lsd-maddrive/bb_project/Чертежи/solid/Крепление переходника 4S.SLDPRT

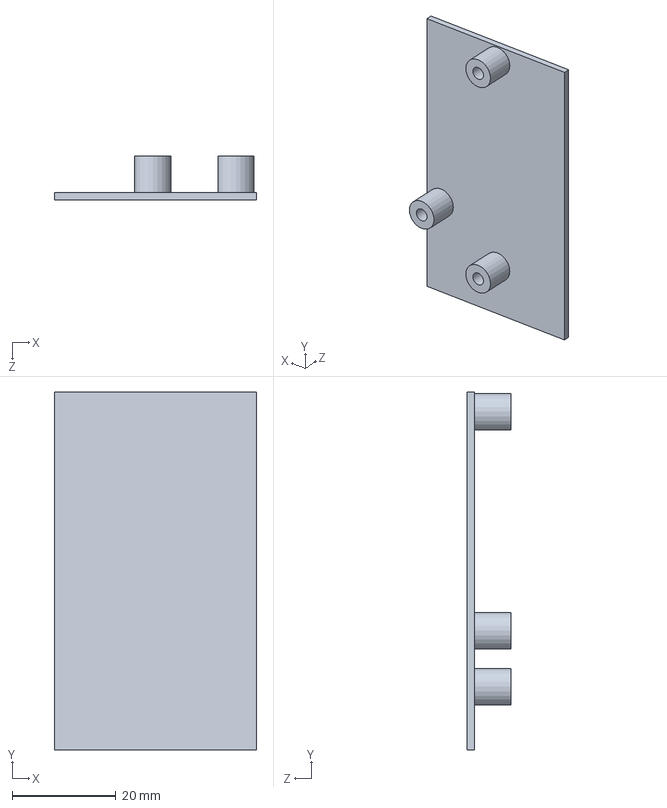
[picture p14: CAD file, 2020-08-11]
Чертежи/solid/Крепление переходника 4S.SLDPRT
39.0 x 69.0 x 8.50 mm
