lsd-maddrive/bb_project/Чертежи/Платформы/Верхняя платформа part1.SLDPRT

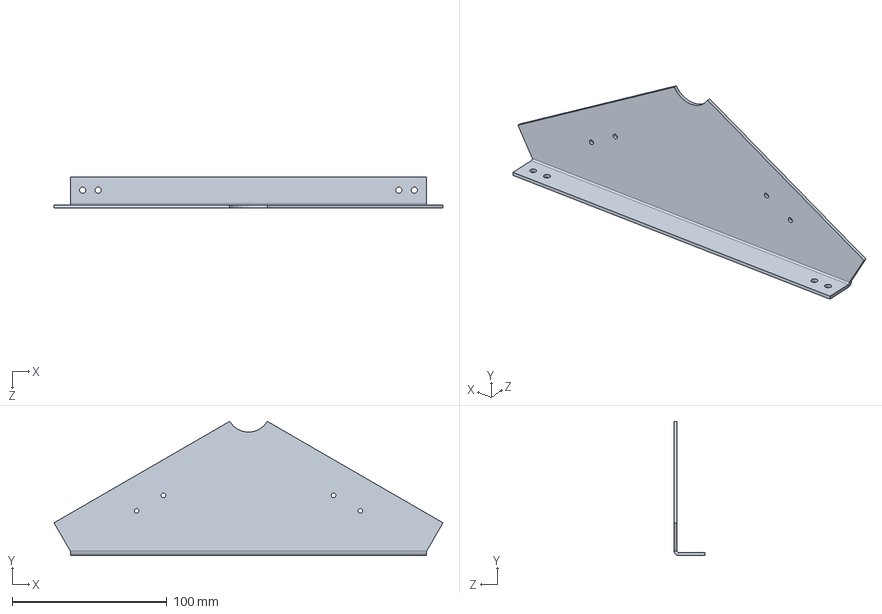
[picture p15: CAD file, 2020-09-08]
Чертежи/Платформы/Верхняя платформа part1.SLDPRT
251.0 x 86.6 x 20.0 mm
