lsd-maddrive/bb_project/Чертежи/solid/Крепление драйвера.SLDPRT

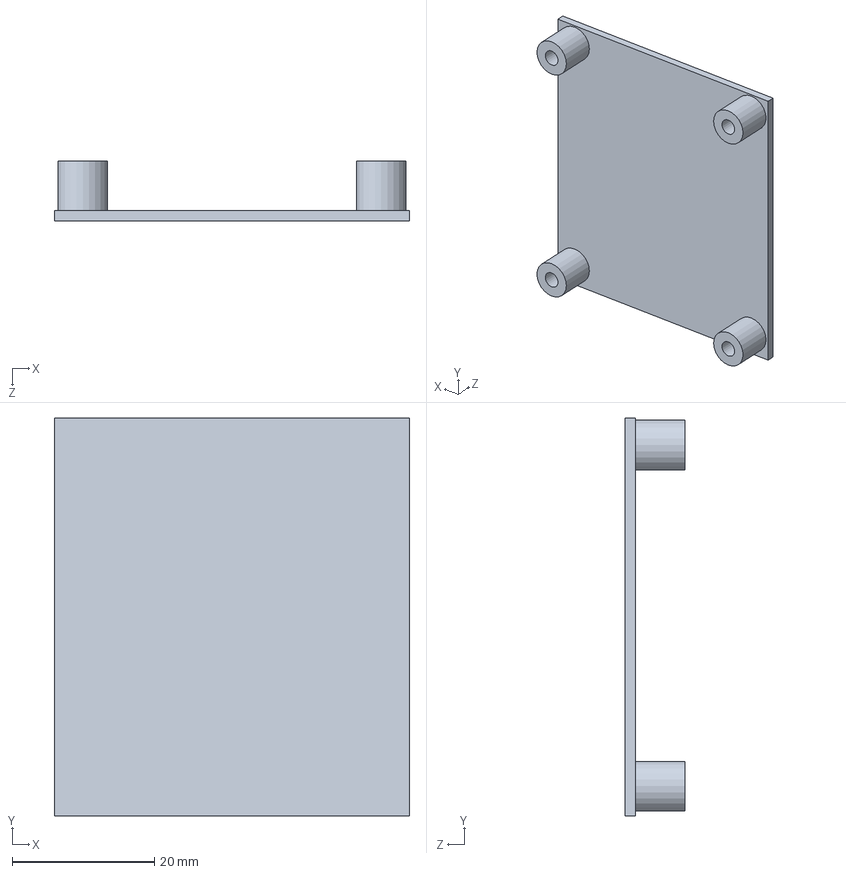
[picture p16: CAD file, 2020-08-11]
Чертежи/solid/Крепление драйвера.SLDPRT
50.0 x 56.0 x 8.50 mm
