lsd-maddrive/bb_project/Чертежи/Платформы/Верхняя платформа (для разделения).SLDPRT

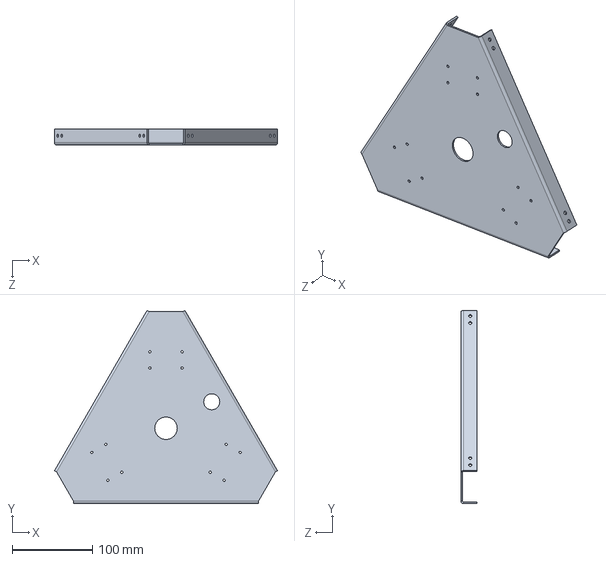
[picture p17: CAD file, 2020-09-08]
Чертежи/Платформы/Верхняя платформа (для разделения).SLDPRT
277.2 x 240.1 x 20.0 mm
