lsd-maddrive/bb_project/Чертежи/Платформы/Драйвер.SLDPRT

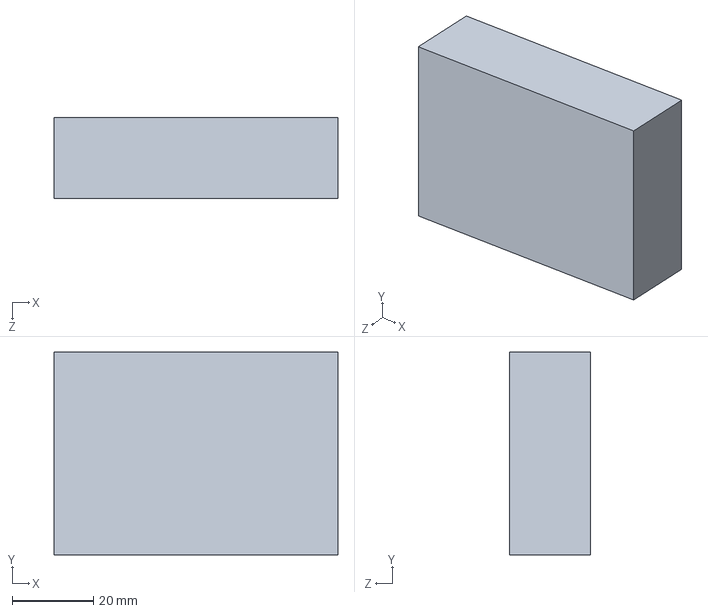
[picture p18: CAD file, 2020-07-24]
Чертежи/Платформы/Драйвер.SLDPRT
70.0 x 50.0 x 20.0 mm
