lsd-maddrive/bb_project/Чертежи/Платформы/батарейка.SLDPRT

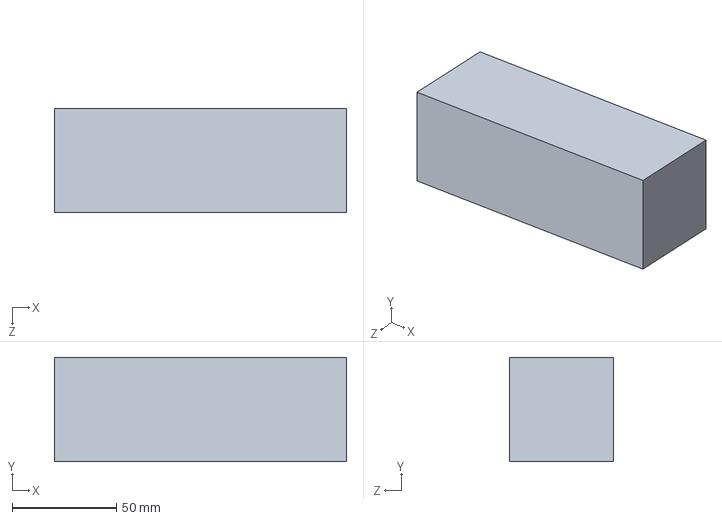
[picture p19: CAD file, 2020-07-24]
Чертежи/Платформы/батарейка.SLDPRT
140.0 x 50.0 x 50.0 mm
