lsd-maddrive/bb_project/Чертежи/Платформы/Нижняя платформа.SLDPRT

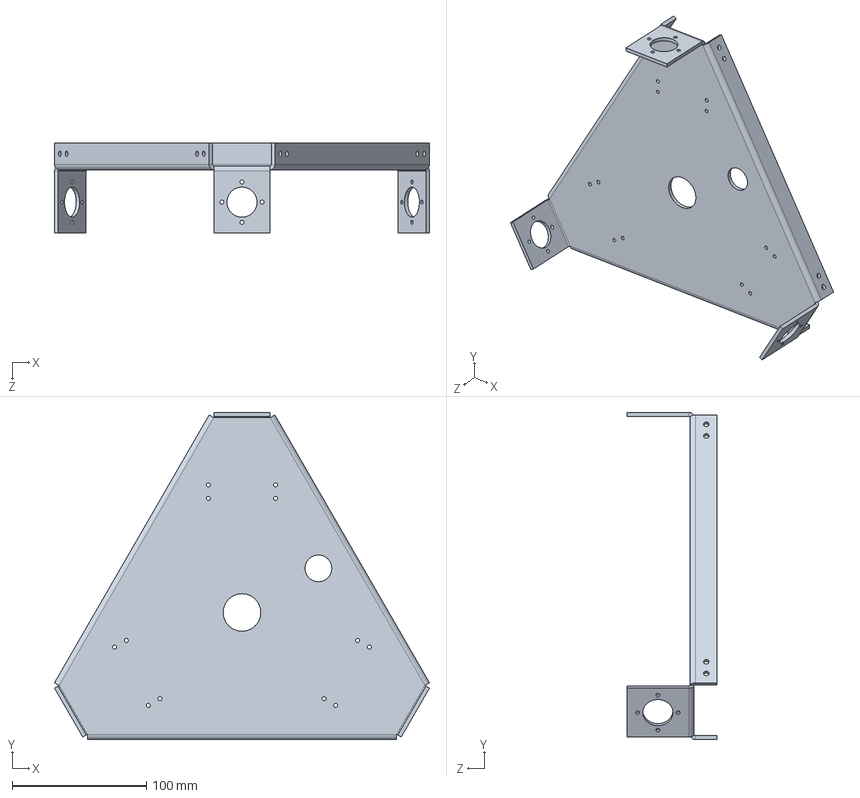
[picture p20: CAD file, 2020-01-11]
Чертежи/Платформы/Нижняя платформа.SLDPRT
278.9 x 243.6 x 67.0 mm
