lsd-maddrive/bb_project/Чертежи/Платформы/Колесо.SLDPRT

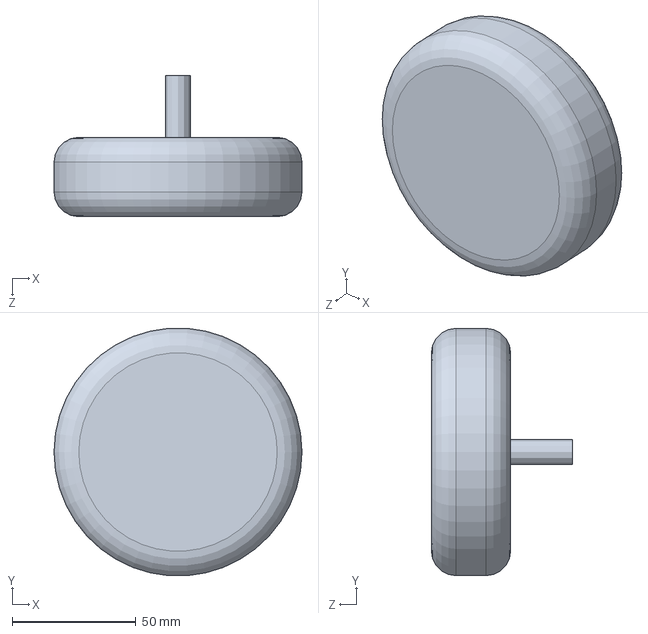
[picture p21: CAD file, 2020-01-11]
Чертежи/Платформы/Колесо.SLDPRT
100.0 x 99.7 x 57.0 mm
