lsd-maddrive/bb_project/Чертежи/Платформы/Motor.SLDPRT

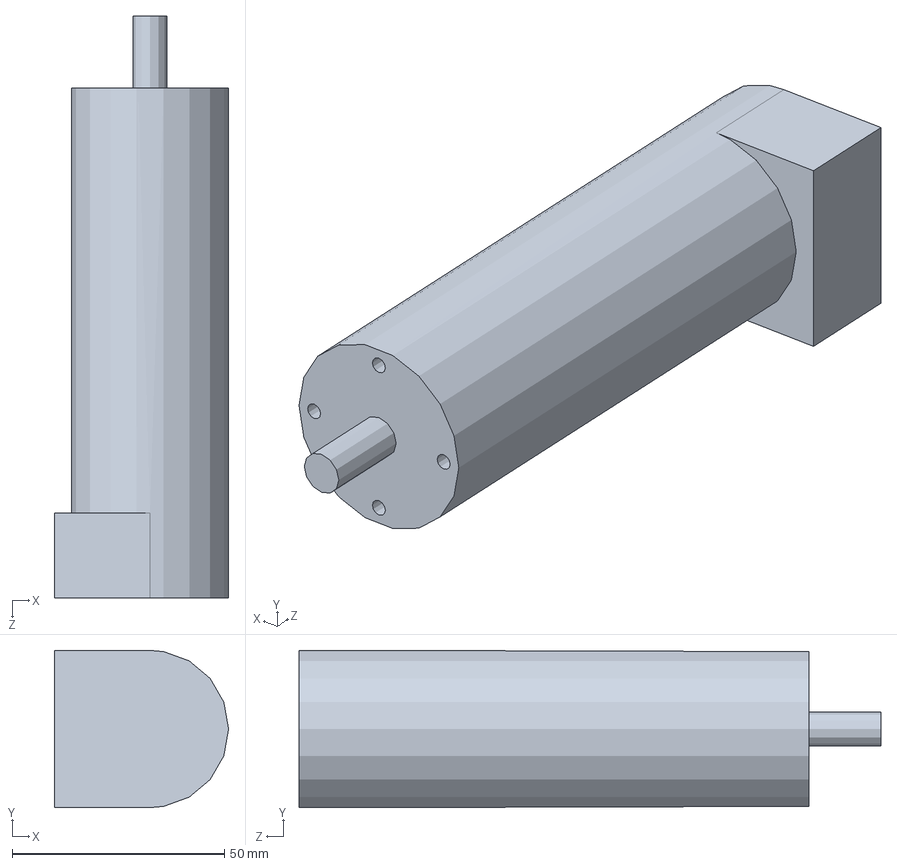
[picture p22: CAD file, 2020-01-11]
Чертежи/Платформы/Motor.SLDPRT
41.0 x 37.0 x 137.0 mm
