lsd-maddrive/bb_project/controller_bb_8_driver/src/i2c.c

#include <i2c.h>


static I2CDriver    *i2cDriver  = &I2CD1;   // Chose i2c hardware driver


static const I2CConfig i2c1conf = {
         STM32_TIMINGR_PRESC(1U)  |
         STM32_TIMINGR_SCLDEL(9U)  | STM32_TIMINGR_SDADEL(9U) |
         STM32_TIMINGR_SCLH(21U)   | STM32_TIMINGR_SCLL(24U),
         0,                         // CR1
         0                          // CR2
};

#define SCL_LINE    PAL_LINE( GPIOB, 8 )
#define DATA_LINE   PAL_LINE( GPIOB, 9 )

uint8_t register_address[1] = {0};


/**
 * @brief   Start hardware i2c module as master
 */
void i2cStartUp(void)
{
    palSetLineMode( SCL_LINE,  PAL_MODE_ALTERNATE(4) | PAL_STM32_OTYPE_OPENDRAIN  );
    palSetLineMode( DATA_LINE, PAL_MODE_ALTERNATE(4) | PAL_STM32_OTYPE_OPENDRAIN );

    i2cStart(i2cDriver, &i2c1conf);
}


/**
 * @brief   Write multiple bytes of data from slave
 * @param
 *          address         7 bit address of slave device
 *          txbuf           link to a buffer array with data to write
 *          length          number of bytes to write
 *          timeout         timeout value [ms]
 *
 * @return                  The operation status.
 * @retval  MSG_OK          if the function succeeded.
 * @retval  MSG_RESET       if one or more I2C errors occurred, the errors can
 *                          be retrieved using @p i2cGetErrors().
 * @retval  MSG_TIMEOUT     if a timeout occurred before operation end.
 */
msg_t i2cSimpleWrite(uint8_t address, uint8_t *txbuf, uint8_t length, uint16_t timeout)
{
    msg_t msg = i2cMasterTransmitTimeout( i2cDriver, address, txbuf, length, NULL, 0, timeout );
    return msg;
}


/**
 * @brief   Read multiple bytes of data from slave
 *
 * @param
 *          address         7 bit address of slave device
 *          rxbuf           link to a buffer array where to store read data
 *          length          number of bytes to read
 *          timeout         timeout value [ms]
 *
 * @return                  The operation status.
 * @retval  MSG_OK          if the function succeeded.
 * @retval  MSG_RESET       if one or more I2C errors occurred, the errors can
 *                          be retrieved using @p i2cGetErrors().
 * @retval  MSG_TIMEOUT     if a timeout occurred before operation end.
 */
msg_t i2cSimpleRead(uint8_t address, uint8_t *rxbuf, uint8_t length, uint16_t timeout)
{
    msg_t msg = i2cMasterReceiveTimeout( i2cDriver, address, rxbuf, length, timeout );
    return msg;
}


/**
 * @brief   Read multiple bytes of data from specific register of slave
 * @details Function writes register address data to slave and then performs
 *          repeated start action with read bit set
 * @param
 *          address         7 bit address of slave device
 *          register_addr   address of register to read
 *          rxbuf           link to a buffer array where to store read data
 *          length          number of bytes to read
 *          timeout         timeout value [ms]
 *
 * @return                  The operation status.
 * @retval  MSG_OK          if the function succeeded.
 * @retval  MSG_RESET       if one or more I2C errors occurred, the errors can
 *                          be retrieved using @p i2cGetErrors().
 * @retval  MSG_TIMEOUT     if a timeout occurred before operation end.
 */
msg_t i2cRegisterRead(uint8_t address, uint8_t register_addr, uint8_t *rxbuf, uint8_t length, uint16_t timeout)
{
    register_address[0] = register_addr;
    msg_t msg = i2cMasterTransmitTimeout( i2cDriver, address, register_address, 1, rxbuf, length, timeout );
    return msg;
}
