lsd-maddrive/bb_project/controller_bb_8_driver/tests/test_robot_odometry.c

#include <tests.h>
#include "robot_odometry.h"


/*
 * @brief   Test robot (kinematic) odometry unit
 */
void testRobotOdometry ( void )
{
    robotOdometryInit();
    robotOdometrySetPermeation( );

    debug_stream_init();

    float       test_v_x    = 0;
    float       test_v_y    = 0;
    float       test_w      = 0;
    float       test_speed  = 0.2f;
    float       test_angle  = 10.0f;

    uint16_t    time_delta  = 100;
    float       time_k      = (float)time_delta * 0.0001;

    systime_t   time = chVTGetSystemTimeX( );
    while( true )
    {
        char rcv_data   = sdGetTimeout( &SD3, TIME_IMMEDIATE );
        switch( rcv_data )
        {
            case 'x':  // change only test_v_x (plus)
              test_v_x = test_speed;
              test_v_y = 0;
              test_w = 0;
              break;

            case 'm':  // change only test_v_x (minus)
              test_v_x = -test_speed;
              test_v_y = 0;
              test_w = 0;
              break;

            case 'y':  // change only test_v_y
              test_v_x = 0;
              test_v_y = test_speed;
              test_w = 0;
              break;

            case 'n':  // change only test_v_y (minus)
              test_v_x = 0;
              test_v_y = -test_speed;
              test_w = 0;
              break;

            case 'w':  // change only test_w (plus)
              test_v_x = 0;
              test_v_y = 0;
              // BE CAREFUL! INTEGRAL OF ANGLE
              test_w += test_angle;
              break;

            case 'q':  // change only test_w (minus)
              test_v_x = 0;
              test_v_y = 0;
              test_w -= test_angle;
              break;

            case ' ':  // full stop
              test_v_x    = 0;
              test_v_y    = 0;
              test_w      = 0;
              break;

            default:
              break;
        }

        robotOdometrySetSpeed( test_v_x, test_v_y, test_w, time_k );

        time = chThdSleepUntilWindowed( time, time + TIME_MS2I( time_delta ) );
    }
}
