lsd-maddrive/bb_project/controller_bb_8_driver/include/tests.h

#ifndef INCLUDE_TESTS_H_
#define INCLUDE_TESTS_H_

#include <common.h>

/*============================================================================*/
/* Motors Control Tests                                                       */
/*============================================================================*/

/*
 * @brief   Test motor direction control
 * @note    Duty cycle is constant
 */
void testRawMotorDirectionControlRoutine( void );

/*
 * @brief   Test raw motor control
 * @note    Duty cycle could be changed [0, 20000]
 *          Stable for incorrect value of duty cycle
 *          Direction is controlled via defines
 *          MOTOR_FORWARD || MOTOR_BACKWARD
 */
void testRawMotorControlRoutine( void );

/*
 * @brief   Test motor control in percents
 * @note    Duty cycle could be changed [-100, 100]
 *          Stable for incorrect value of duty cycle
 *          >= 0        FORWARD
 *           < 0        BACKWARD
 */
void testMotorControlRoutine( void );

/**
 * @brief   Find out the correct frequency for motors (via Matlab)
 * @note    Test only for motor A.
 *          Consumption:
 *              all motors are similar,
 *              and configuration for motor A works for motor B and C
 */
void testMatlabFrequency( void );

/*============================================================================*/
/* Encoder Tests                                                              */
/*============================================================================*/

/**
 * @brief   Test common encoder routine
 * @note    Print number of ticks, (int)revs and state of direction
 *          0   - clockwise
 *          1   - counterclockwise
 */
void testEncoderRoutine( void );

/*============================================================================*/
/* Wheel Odometry Tests                                                       */
/*============================================================================*/

/*
 * @brief   Test motor speed
 */
void testMotorSpeed( void );

/*
 * @brief   Test wheel speed
 */
void testWheelSpeed( void );

/*
 * @brief   Test linear robot speed calculation in Matlab
 */
void testLinearSpeedMatlab( void );

/*============================================================================*/
/* Robot Odometry Tests (kinematic)                                           */
/*============================================================================*/

/*
 * @brief   Test robot (kinematic) odometry unit
 */
void testRobotOdometry ( void );

/*============================================================================*/
/* Wheel Control System Tests                                                 */
/*============================================================================*/

/*
 * @brief   Test wheel control system with matlab
 */
void testWheelControlMatlab( void );


/*
 * @brief   Test wheel control system with matlab
 * @note    Send two packages with float value (4-byte)
 *          only wheel A data are send to matlab
 */
void testOneWheelControllerMatlab( void );

/*============================================================================*/
/* Gyroscope Tests                                                            */
/*============================================================================*/

/*
 * @brief   Test gyroscope L3GD20H library
 */
void testGyroscope(void);

/*============================================================================*/
/* Joystick Tests                                                             */
/*============================================================================*/

/*
 * @brief   Simple joystick test (without control system)
 */
void testJoystick( void );


/*
 * @brief   Test control robot via joystick
 * @note    Data transferring via USB (SD3)
 * */
void testRobotWithJoystick( void );

/*============================================================================*/
/* Logger Tests                                                               */
/*============================================================================*/

/*
 * @brief   Test sending log data to Python
 * @note    Data transferring via UART (SD6)
 * */
void testLogger(void);

#endif /* INCLUDE_TESTS_H_ */
