lsd-maddrive/bb_project/controller_bb_8_driver/tests/test_joystick.c

#include "tests.h"
#include "robot_odometry.h"
#include "lld_gyroscope.h"
#include "logger.h"
#include "lld_control.h"

static const SerialConfig sdcfg = {
  .speed = 115200,
  .cr1 = 0, .cr2 = 0, .cr3 = 0
};

/*
 * @brief   Simple joystick test (without control system)
 */
void testJoystick( void )
{
    debug_stream_init();

    sdStart( &SD6, &sdcfg );
    palSetPadMode( GPIOG, 14, PAL_MODE_ALTERNATE(8) );   // TX
    palSetPadMode( GPIOG, 9,  PAL_MODE_ALTERNATE(8) );   // RX

    float buf[3] = {0, 0, 0};

    systime_t   time = chVTGetSystemTimeX( );
    while( true )
    {
        sdReadTimeout( &SD3, (uint8_t*) &buf, 12, TIME_IMMEDIATE );

        chprintf( (BaseSequentialStream *)&SD6, "x: %d\ty: %d\tw: %d\n\r",
                  (int32_t)(buf[0] * 100),
                  (int32_t)(buf[1] * 100),
                  (int32_t)(buf[2] * 100)
                  );

        time = chThdSleepUntilWindowed( time, time + TIME_MS2I( 100 ) );
    }
}

/*
 * @brief   Test control robot via joystick
 * @note    Data transferring via USB (SD3)
 *
 * */
void testRobotWithJoystick( void )
{
    debug_stream_init();
    robotOdometryInit();

    uint16_t    time_delta  = 100;
    uint8_t     start_cmd = 0;

    while( (int)start_cmd != 185 )
    {
        start_cmd = sdGet( &SD3 );
    }

    robotOdometrySetPermeation( );

    float log[13] = {0, 0, 0, 0, 0, 0, 0, 0, 0, 0, 0, 0, 0};
    float buf[3] = {0, 0, 0};

    float       time_k      = (float)time_delta * 0.001;

    systime_t   time = chVTGetSystemTime( );
    while( true )
    {
      sdReadTimeout( &SD3, (uint8_t*) &buf, 12, TIME_IMMEDIATE );

      // 0.1 = 100 ms -> 1 ms
      robotOdometrySetSpeed(buf[0], buf[1], buf[2], time_k );

      //Send all data to python
      log[0] = (float)chVTGetSystemTime( );
      log[1] = robotOdometryGetAngleIntegral();
      log[2] = getGyroAngle( GYRO_AXIS_X );
      log[3] = getGyroAngle( GYRO_AXIS_Y );
      log[4] = getGyroAngle( GYRO_AXIS_Z );
      log[5] = buf[0];
      log[6] = buf[1];
      log[7] = buf[2];
      log[8] = robotOdometryGetVelocityXLocal();
      log[9] = robotOdometryGetVelocityYLocal();
      log[10] = odometryGetWheelSpeed(A, REVS_PER_SEC);
      log[11] = odometryGetWheelSpeed(B, REVS_PER_SEC);
      log[12] = odometryGetWheelSpeed(C, REVS_PER_SEC);

      sendLog( &SD3, log, 13);

      time = chThdSleepUntilWindowed( time, time + TIME_MS2I( time_delta ) );
    }
}
